JamieK0/E-paper-Clock/Images/IMG_1409.jpg

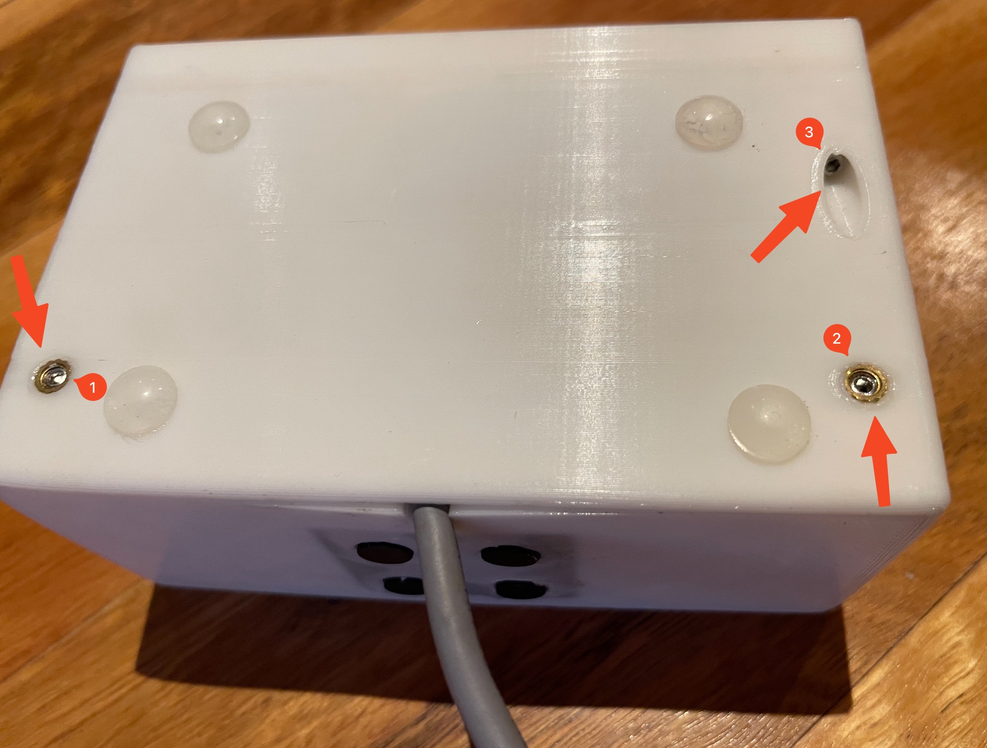
Images/IMG_1409.jpg
